Breadstick-Innovations/Raspberry-Breadstick/RP2040-Breadstick/Snap EDA/LM66200DRLR/LM66200DRLR.stp

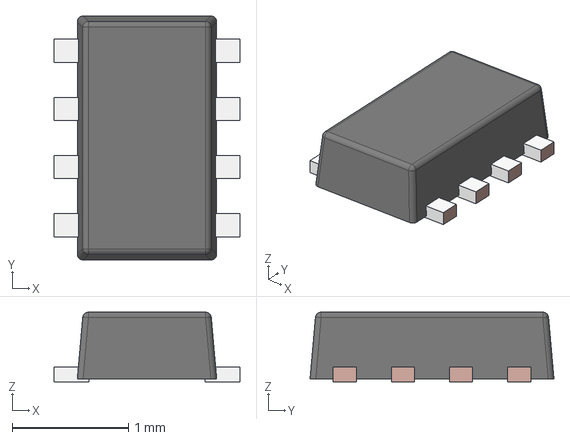
[picture p25: CAD file, 2023-11-04]
RP2040-Breadstick/Snap EDA/LM66200DRLR/LM66200DRLR.stp
1.60 x 2.10 x 0.6 mm
FRAME-DRL0008A
BODY-SOT
