Breadstick-Innovations/Raspberry-Breadstick/RP2040-Breadstick/Snap EDA/USB-C-2171790001/2171790001.stp

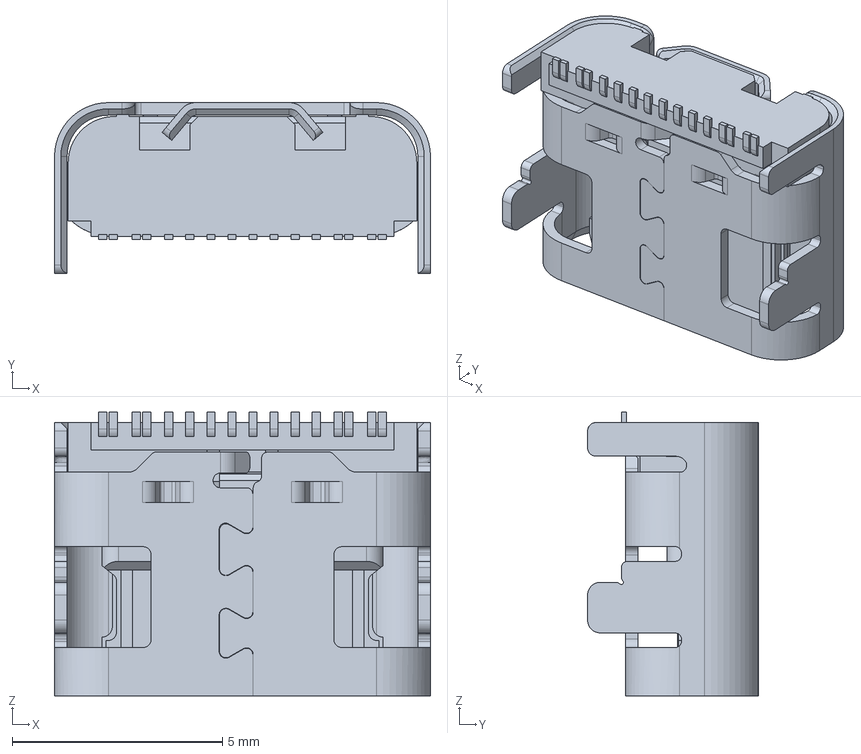
[picture p26: CAD file, 2023-03-05]
RP2040-Breadstick/Snap EDA/USB-C-2171790001/2171790001.stp
8.94 x 4.06 x 6.75 mm
