Breadstick-Innovations/Raspberry-Breadstick/RP2040-Breadstick/Snap EDA/SK9822-2020 RGB LED v2_old.step

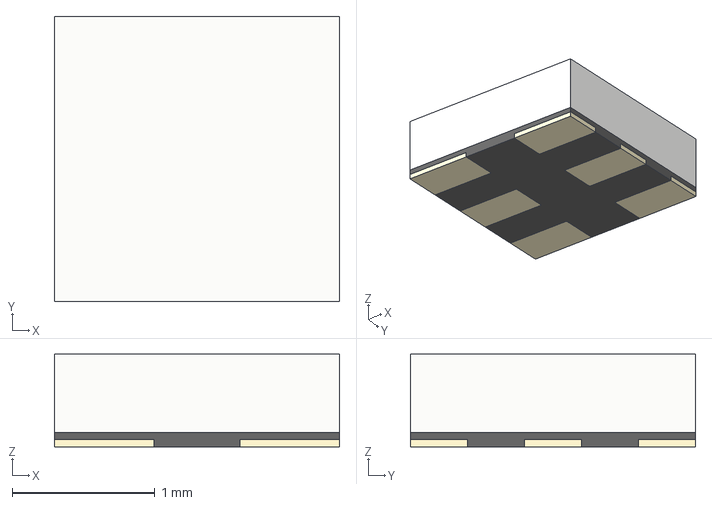
[picture p27: CAD file, 2022-07-29, an earlier design]
RP2040-Breadstick/Snap EDA/SK9822-2020 RGB LED v2_old.step
2.00 x 2.00 x 0.65 mm
