Breadstick-Innovations/Raspberry-Breadstick/Demo Code - rev0.2/CircuitPython/6-Axis IMU/code.py

import time
import board
import digitalio
import busio
##Gyro
from adafruit_lsm6ds import Rate, AccelRange, GyroRange
# from adafruit_lsm6ds.lsm6dsox import LSM6DSOX as LSM6DS
# from adafruit_lsm6ds.lsm6ds33 import LSM6DS33 as LSM6DS
# from adafruit_lsm6ds.lsm6dso32 import LSM6DSO32 as LSM6DS
# from adafruit_lsm6ds.ism330dhcx import ISM330DHCX as LSM6DS
from adafruit_lsm6ds.lsm6ds3trc import LSM6DS3TRC as LSM6DS

# definitions
IMU_SCL = board.GP17
IMU_SDA = board.GP16


### setup Gyro
i2c = busio.I2C(IMU_SCL,IMU_SDA)
sensor = LSM6DS(i2c)

sensor.accelerometer_range = AccelRange.RANGE_4G
print("Accelerometer range set to: %d G" % AccelRange.string[sensor.accelerometer_range])

sensor.gyro_range = GyroRange.RANGE_1000_DPS
print("Gyro range set to: %d DPS" % GyroRange.string[sensor.gyro_range])

sensor.accelerometer_data_rate = Rate.RATE_1_66K_HZ
print("Accelerometer rate set to: %d HZ" % Rate.string[sensor.accelerometer_data_rate])

sensor.gyro_data_rate = Rate.RATE_1_66K_HZ
print("Gyro rate set to: %d HZ" % Rate.string[sensor.gyro_data_rate])


## Gyro not reqired for Pedometer
#sensor.gyro_data_rate = Rate.RATE_SHUTDOWN
## Enable pedometer
#sensor.pedometer_enable = True


while True:
    ##pedometer
    #print("Steps: ", sensor.pedometer_steps)
    #time.sleep(1)

    #print(sensor.temperature)

    acc_x, acc_y, acc_z = sensor.acceleration
    gyro_x, gyro_z, gyro_z = sensor.gyro

    ### accel and Gyro stuff
    # print(
        # "Accel X:%.2f Y:%.2f Z:%.2f ms^2 Gyro X:%.2f Y:%.2f Z:%.2f radians/s"
        # % (sensor.acceleration + sensor.gyro)
    # )

    #print(sensor.acceleration)
    print(acc_y)
    # print(sensor.gyro)

    # print("(%f, %f, %f, %f, %f, %f)" % (sensor.acceleration + sensor.gyro))




    time.sleep(0.05)
